holla2040/solohm/electronicLoadCC3200/board/testing/150201 - 190W panel SolOhm Dashboard.png

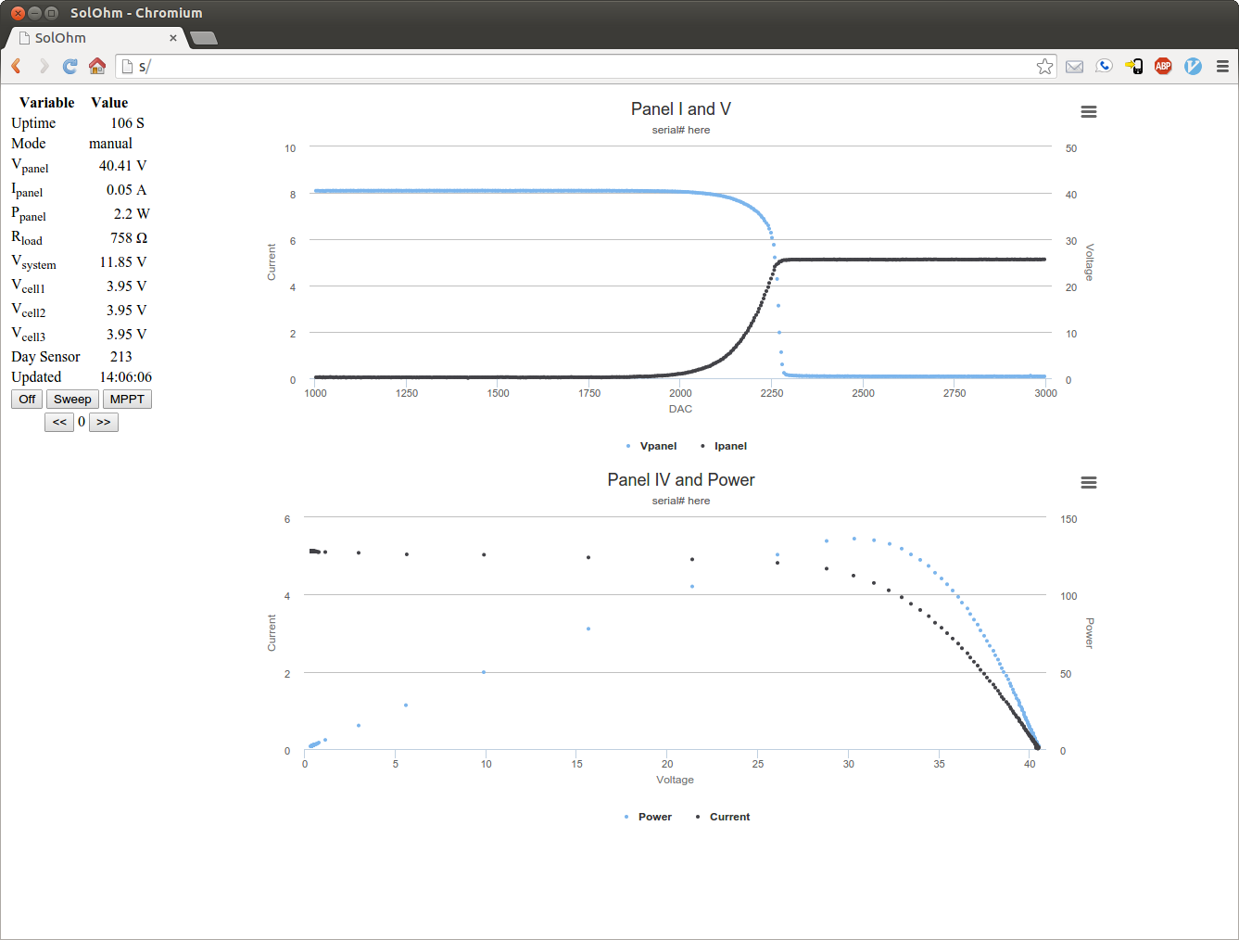
electronicLoadCC3200/board/testing/150201 - 190W panel SolOhm Dashboard.png
